facebookarchive/RiftDK1/Firmware/stm32_it.c

/**
  ******************************************************************************
  * @file    stm32_it.c
  * @author  MCD Application Team
  * @version V3.4.0
  * @date    29-June-2012
  * @brief   Main Interrupt Service Routines.
  *          This file provides template for all exceptions handler and peripherals
  *          interrupt service routine.
  ******************************************************************************
  * @attention
  *
  * <h2><center>&copy; COPYRIGHT 2012 STMicroelectronics</center></h2>
  *
  * Licensed under MCD-ST Liberty SW License Agreement V2, (the "License");
  * You may not use this file except in compliance with the License.
  * You may obtain a copy of the License at:
  *
  *        http://www.st.com/software_license_agreement_liberty_v2
  *
  * Unless required by applicable law or agreed to in writing, software
  * distributed under the License is distributed on an "AS IS" BASIS,
  * WITHOUT WARRANTIES OR CONDITIONS OF ANY KIND, either express or implied.
  * See the License for the specific language governing permissions and
  * limitations under the License.
  *
  ******************************************************************************
  */


/* Includes ------------------------------------------------------------------*/

#include "stm32_it.h"
#include "usb_istr.h"
#include "usb_lib.h"
#include "usb_pwr.h"
#include "hw_config.h"
#include "delay.h"
#include "uart.h"
#include "invensense.h"

/* Private typedef -----------------------------------------------------------*/
/* Private define ------------------------------------------------------------*/
/* Private macro -------------------------------------------------------------*/
/* Private variables ---------------------------------------------------------*/
extern __IO uint32_t int_count_inv;
extern __IO uint32_t int_count_hmc;
extern __IO uint8_t exit_stop_mode;
/* Private function prototypes -----------------------------------------------*/
/* Private functions ---------------------------------------------------------*/

/******************************************************************************/
/*            Cortex-M Processor Exceptions Handlers                         */
/******************************************************************************/

/*******************************************************************************
* Function Name  : NMI_Handler
* Description    : This function handles NMI exception.
* Input          : None
* Output         : None
* Return         : None
*******************************************************************************/
void NMI_Handler(void)
{
}

/*******************************************************************************
* Function Name  : HardFault_Handler
* Description    : This function handles Hard Fault exception.
* Input          : None
* Output         : None
* Return         : None
*******************************************************************************/
void HardFault_Handler(void)
{
  /* Go to infinite loop when Hard Fault exception occurs */
  while (1)
  {
  }
}

/*******************************************************************************
* Function Name  : MemManage_Handler
* Description    : This function handles Memory Manage exception.
* Input          : None
* Output         : None
* Return         : None
*******************************************************************************/
void MemManage_Handler(void)
{
  /* Go to infinite loop when Memory Manage exception occurs */
  while (1)
  {
  }
}

/*******************************************************************************
* Function Name  : BusFault_Handler
* Description    : This function handles Bus Fault exception.
* Input          : None
* Output         : None
* Return         : None
*******************************************************************************/
void BusFault_Handler(void)
{
  /* Go to infinite loop when Bus Fault exception occurs */
  while (1)
  {
  }
}

/*******************************************************************************
* Function Name  : UsageFault_Handler
* Description    : This function handles Usage Fault exception.
* Input          : None
* Output         : None
* Return         : None
*******************************************************************************/
void UsageFault_Handler(void)
{
  /* Go to infinite loop when Usage Fault exception occurs */
  while (1)
  {
  }
}

/*******************************************************************************
* Function Name  : SVC_Handler
* Description    : This function handles SVCall exception.
* Input          : None
* Output         : None
* Return         : None
*******************************************************************************/
void SVC_Handler(void)
{
}

/*******************************************************************************
* Function Name  : DebugMon_Handler
* Description    : This function handles Debug Monitor exception.
* Input          : None
* Output         : None
* Return         : None
*******************************************************************************/
void DebugMon_Handler(void)
{
}

/*******************************************************************************
* Function Name  : PendSV_Handler
* Description    : This function handles PendSVC exception.
* Input          : None
* Output         : None
* Return         : None
*******************************************************************************/
void PendSV_Handler(void)
{
}

/*******************************************************************************
* Function Name  : SysTick_Handler
* Description    : This function handles SysTick Handler.
* Input          : None
* Output         : None
* Return         : None
*******************************************************************************/
void SysTick_Handler(void)
{
  delay_update();
}

/******************************************************************************/
/*            STM32 Peripherals Interrupt Handlers                        */
/******************************************************************************/
#ifndef STM32F10X_CL
/*******************************************************************************
* Function Name  : USB_IRQHandler
* Description    : This function handles USB Low Priority interrupts
*                  requests.
* Input          : None
* Output         : None
* Return         : None
*******************************************************************************/
#if defined(STM32L1XX_MD) || defined(STM32L1XX_HD)|| defined(STM32L1XX_MD_PLUS)
void USB_LP_IRQHandler(void)
#else
void USB_LP_CAN1_RX0_IRQHandler(void)
#endif
{
  USB_Istr();
}
#endif /* STM32F10X_CL */

void USBWakeUp_IRQHandler(void)
{
    exit_stop_mode = 1;
    EXTI_ClearITPendingBit(EXTI_Line18);
}

void USART1_IRQHandler(void)
{
    uart_receive(USART1);
}

void USART2_IRQHandler(void)
{
    uart_receive(USART2);
}

void USART3_IRQHandler(void)
{
    uart_receive(USART3);
}

/*******************************************************************************
* Function Name  : EXTI_IRQHandler
* Description    : This function handles External lines interrupt request.
* Input          : None
* Output         : None
* Return         : None
*******************************************************************************/
void EXTI0_IRQHandler(void)
{
  if (EXTI_GetITStatus(INV_INT_LINE) != RESET) {
    // If this was a motion interrupt
    if (invensense_motion_interrupt()) {
        // And remote wakeup is enabled (ClearFeature didn't happen)
        if (pInformation->Current_Feature & 0x20) {
            exit_stop_mode = 2;
        }
    } else {
      // otherwise this was just a normal data ready interrupt
      int_count_inv++;
    }

    EXTI_ClearITPendingBit(INV_INT_LINE);
  }
}

#if defined(USE_STEVAL_MKI121V1)
void EXTI3_IRQHandler(void)
#else /* USE_TRACKER_V1 */
void EXTI1_IRQHandler(void)
#endif
{
  if (EXTI_GetITStatus(HMC_INT_LINE) != RESET) {
    int_count_hmc++;
    EXTI_ClearITPendingBit(HMC_INT_LINE);
  }
}

/******************************************************************************/
/*                 STM32 Peripherals Interrupt Handlers                   */
/*  Add here the Interrupt Handler for the used peripheral(s) (PPP), for the  */
/*  available peripheral interrupt handler's name please refer to the startup */
/*  file (startup_stm32xxx.s).                                            */
/******************************************************************************/

/*******************************************************************************
* Function Name  : PPP_IRQHandler
* Description    : This function handles PPP interrupt request.
* Input          : None
* Output         : None
* Return         : None
*******************************************************************************/
/*void PPP_IRQHandler(void)
{
}*/

/************************ (C) COPYRIGHT STMicroelectronics *****END OF FILE****/
